mosquitorgnole/lesonar2/lesonar2_software/colormap.h

const float viridis[256][3] = {
    {0.267004, 0.004874, 0.329415},
    {0.268510, 0.009605, 0.335427},
    {0.269944, 0.014625, 0.341379},
    {0.271305, 0.019942, 0.347269},
    {0.272594, 0.025563, 0.353093},
    {0.273809, 0.031497, 0.358853},
    {0.274952, 0.037752, 0.364543},
    {0.276022, 0.044167, 0.370164},
    {0.277018, 0.050344, 0.375715},
    {0.277941, 0.056324, 0.381191},
    {0.278791, 0.062145, 0.386592},
    {0.279566, 0.067836, 0.391917},
    {0.280267, 0.073417, 0.397163},
    {0.280894, 0.078907, 0.402329},
    {0.281446, 0.084320, 0.407414},
    {0.281924, 0.089666, 0.412415},
    {0.282327, 0.094955, 0.417331},
    {0.282656, 0.100196, 0.422160},
    {0.282910, 0.105393, 0.426902},
    {0.283091, 0.110553, 0.431554},
    {0.283197, 0.115680, 0.436115},
    {0.283229, 0.120777, 0.440584},
    {0.283187, 0.125848, 0.444960},
    {0.283072, 0.130895, 0.449241},
    {0.282884, 0.135920, 0.453427},
    {0.282623, 0.140926, 0.457517},
    {0.282290, 0.145912, 0.461510},
    {0.281887, 0.150881, 0.465405},
    {0.281412, 0.155834, 0.469201},
    {0.280868, 0.160771, 0.472899},
    {0.280255, 0.165693, 0.476498},
    {0.279574, 0.170599, 0.479997},
    {0.278826, 0.175490, 0.483397},
    {0.278012, 0.180367, 0.486697},
    {0.277134, 0.185228, 0.489898},
    {0.276194, 0.190074, 0.493001},
    {0.275191, 0.194905, 0.496005},
    {0.274128, 0.199721, 0.498911},
    {0.273006, 0.204520, 0.501721},
    {0.271828, 0.209303, 0.504434},
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
};



const float inferno[256][3] = {
    {0.001462, 0.000466, 0.013866},
    {0.002267, 0.001270, 0.018570},
    {0.003299, 0.002249, 0.024239},
    {0.004547, 0.003392, 0.030909},
    {0.006006, 0.004692, 0.038558},
    {0.007676, 0.006136, 0.046836},
    {0.009561, 0.007713, 0.055143},
    {0.011663, 0.009417, 0.063460},
    {0.013995, 0.011225, 0.071862},
    {0.016561, 0.013136, 0.080282},
    {0.019373, 0.015133, 0.088767},
    {0.022447, 0.017199, 0.097327},
    {0.025793, 0.019331, 0.105930},
    {0.029432, 0.021503, 0.114621},
    {0.033385, 0.023702, 0.123397},
    {0.037668, 0.025921, 0.132232},
    {0.042253, 0.028139, 0.141141},
    {0.046915, 0.030324, 0.150164},
    {0.051644, 0.032474, 0.159254},
    {0.056449, 0.034569, 0.168414},
    {0.061340, 0.036590, 0.177642},
    {0.066331, 0.038504, 0.186962},
    {0.071429, 0.040294, 0.196354},
    {0.076637, 0.041905, 0.205799},
    {0.081962, 0.043328, 0.215289},
    {0.087411, 0.044556, 0.224813},
    {0.092990, 0.045583, 0.234358},
    {0.098702, 0.046402, 0.243904},
    {0.104551, 0.047008, 0.253430},
    {0.110536, 0.047399, 0.262912},
    {0.116656, 0.047574, 0.272321},
    {0.122908, 0.047536, 0.281624},
    {0.129285, 0.047293, 0.290788},
    {0.135778, 0.046856, 0.299776},
    {0.142378, 0.046242, 0.308553},
    {0.149073, 0.045468, 0.317085},
    {0.155850, 0.044559, 0.325338},
    {0.162689, 0.043554, 0.333277},
    {0.169575, 0.042489, 0.340874},
    {0.176493, 0.041402, 0.348111},
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
};
